jorgeflorestn/CircuitoTactil1/Gerbers/cotizacion.jpg

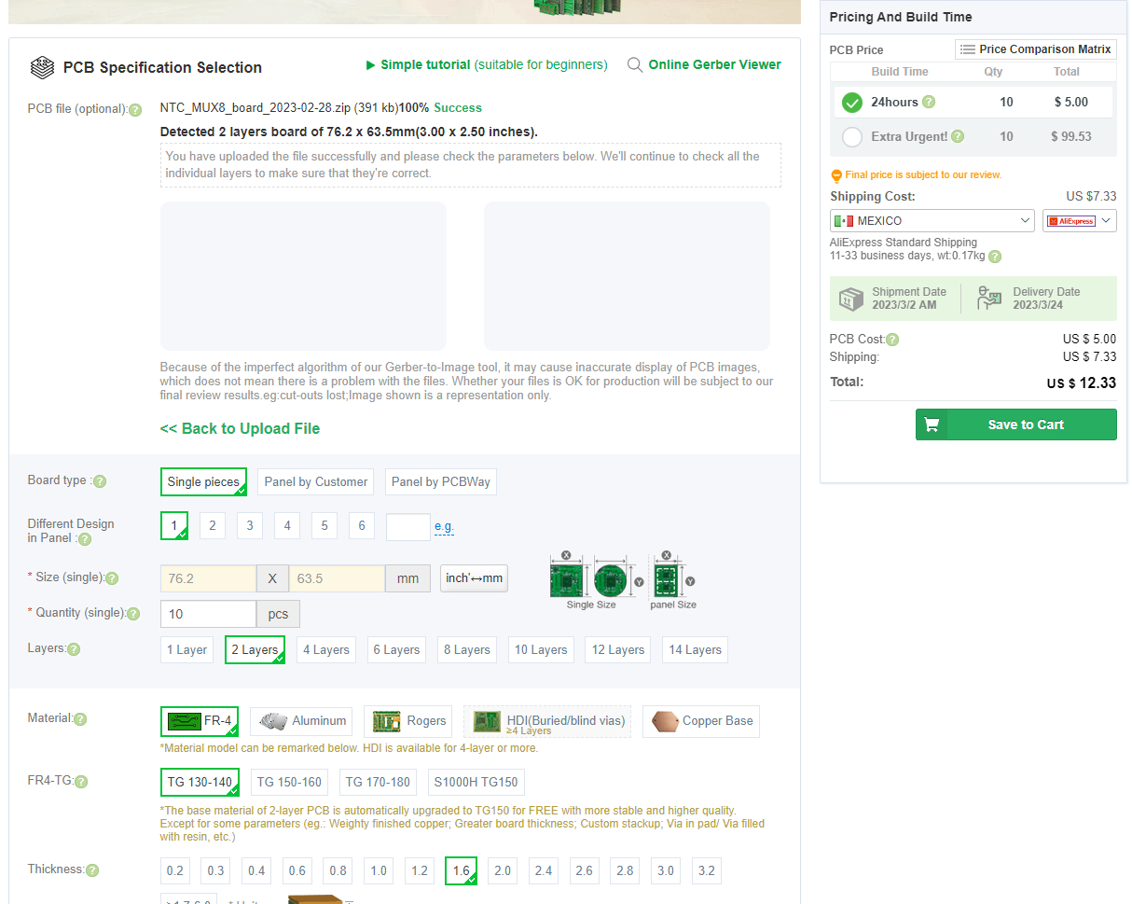
Gerbers/cotizacion.jpg
