jorgeflorestn/CircuitoTactil1/Pictures/Diagrams/4K1Zo.png

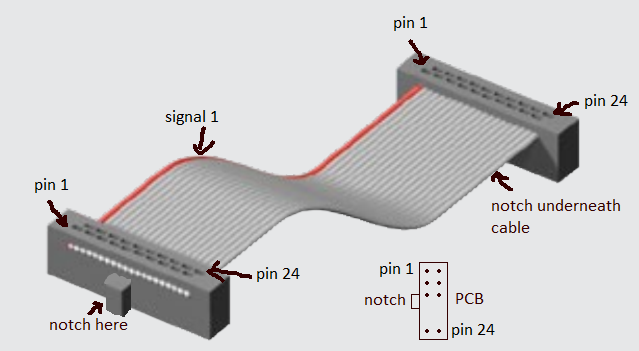
Pictures/Diagrams/4K1Zo.png
