jorgeflorestn/CircuitoTactil1/Pictures/Diagrams/2023-02-26_175827.jpg

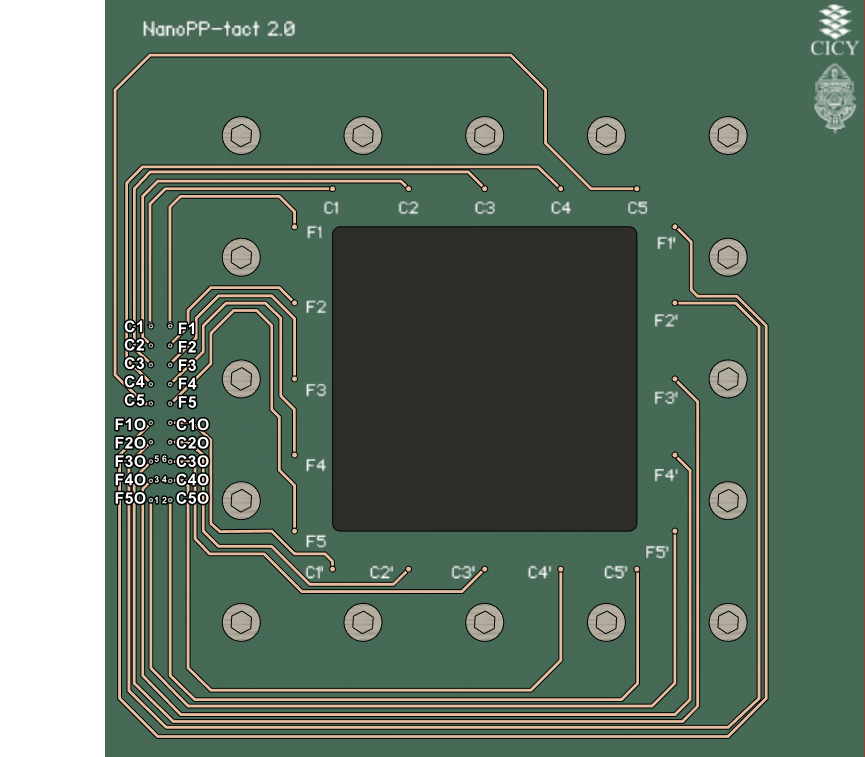
Pictures/Diagrams/2023-02-26_175827.jpg
