jorgeflorestn/CircuitoTactil1/Pictures/Diagrams/20230223_190704.jpg

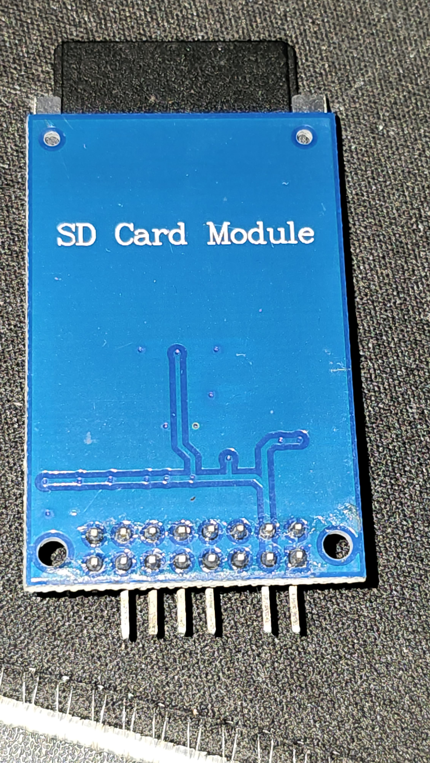
Pictures/Diagrams/20230223_190704.jpg
