jorgeflorestn/CircuitoTactil1/Pictures/Diagrams/20230223_190718.jpg

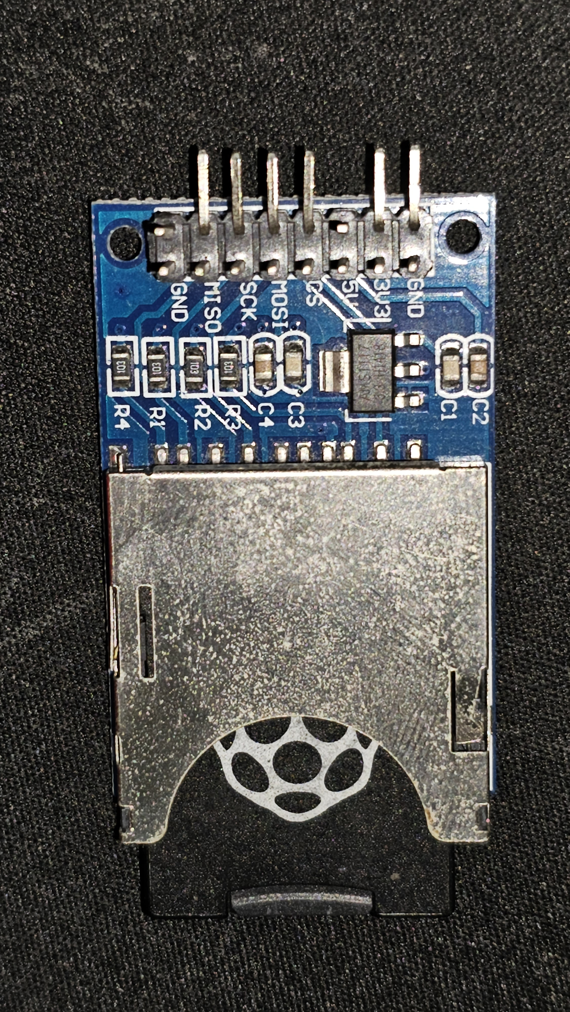
Pictures/Diagrams/20230223_190718.jpg
