jorgeflorestn/CircuitoTactil1/Pictures/Diagrams/circuit1.png

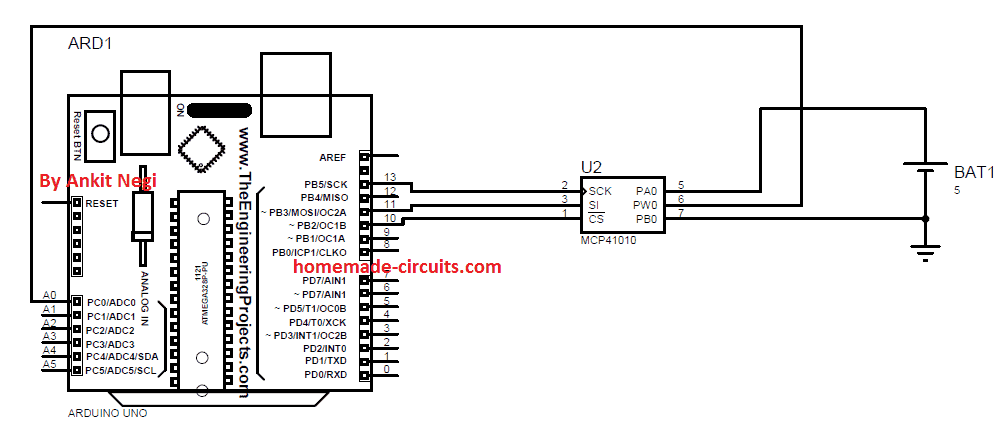
Pictures/Diagrams/circuit1.png
