jorgeflorestn/CircuitoTactil1/Pictures/Diagrams/MicrosoftTeams-image.png

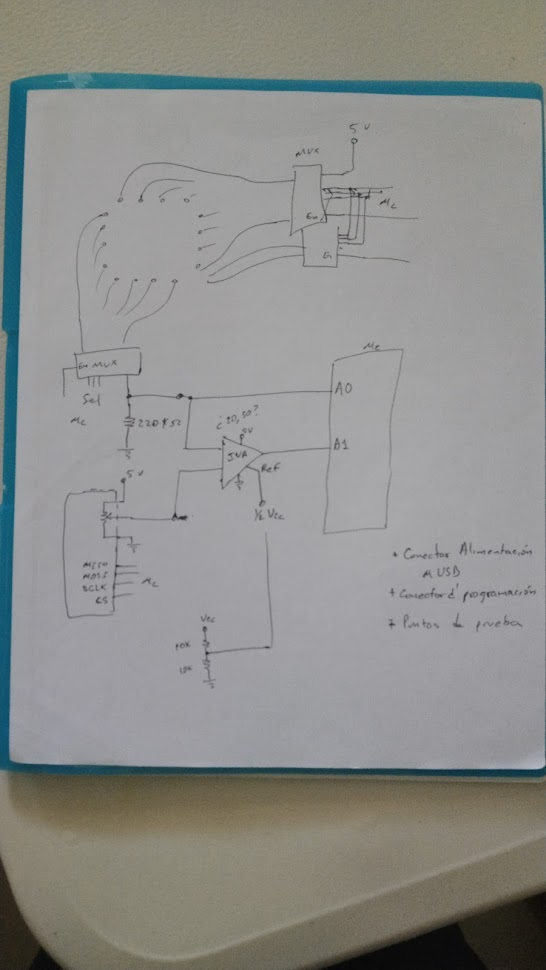
Pictures/Diagrams/MicrosoftTeams-image.png
