jorgeflorestn/CircuitoTactil1/Pictures/Diagrams/SD.jpeg

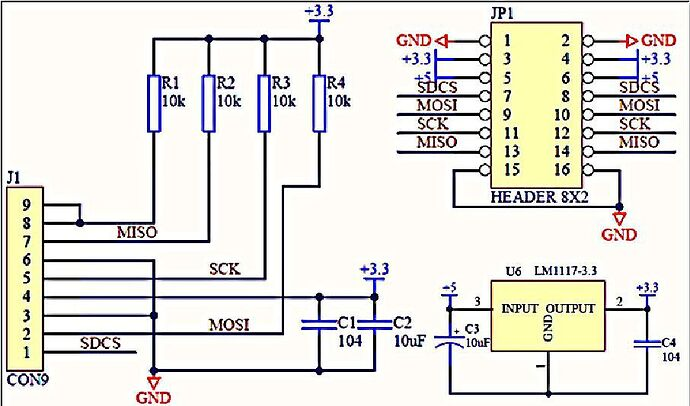
Pictures/Diagrams/SD.jpeg
