jorgeflorestn/CircuitoTactil1/Pictures/Diagrams/WhatsApp Image 2023-02-15 at 4.53.52 PM.jpeg

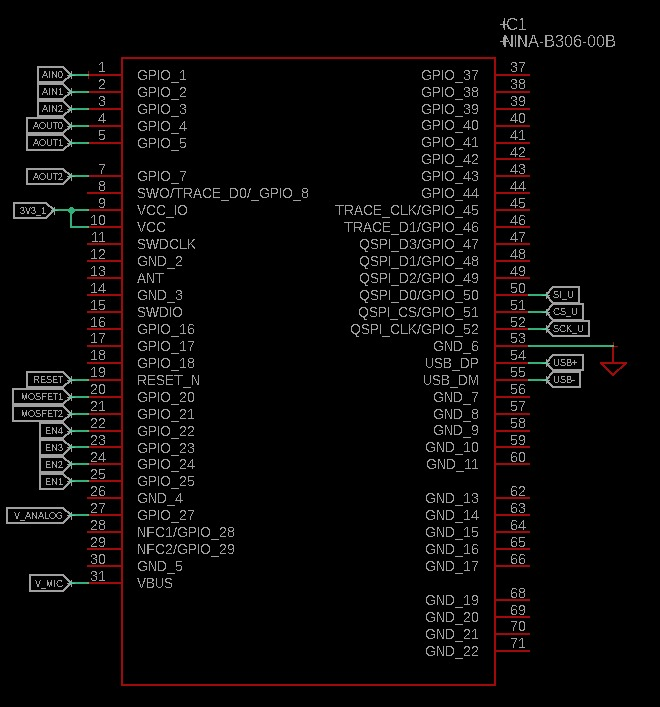
Pictures/Diagrams/WhatsApp Image 2023-02-15 at 4.53.52 PM.jpeg
