jorgeflorestn/CircuitoTactil1/Pictures/MicrosoftTeams-image (1).png

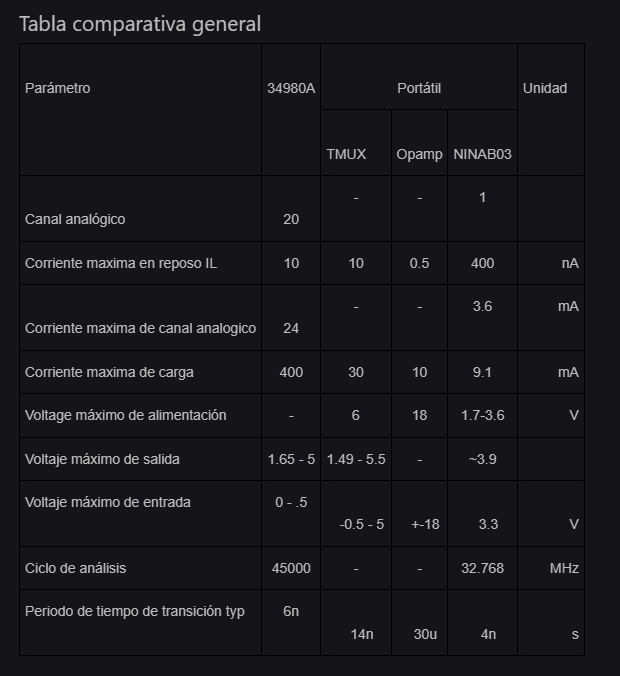
Pictures/MicrosoftTeams-image (1).png
