jorgeflorestn/CircuitoTactil1/Pictures/NTC_MUX8_board_2023-Feb-27_10-32-54AM-000_CustomizedView22131778855.png

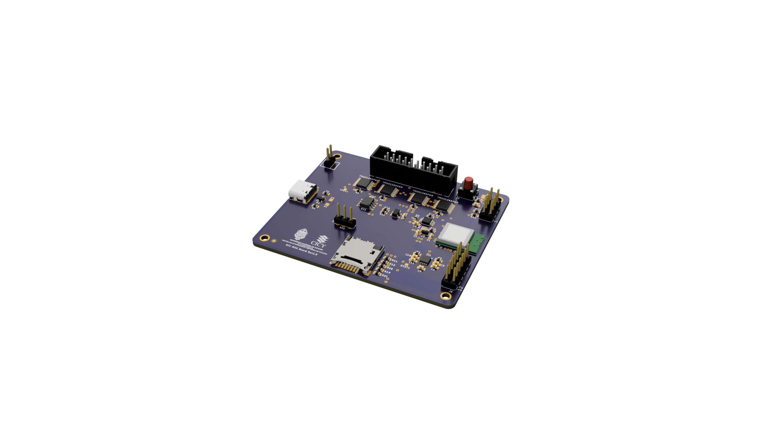
Pictures/NTC_MUX8_board_2023-Feb-27_10-32-54AM-000_CustomizedView22131778855.png
